FixturFab/fixture_switch_reader/images/bottom case cad.JPG

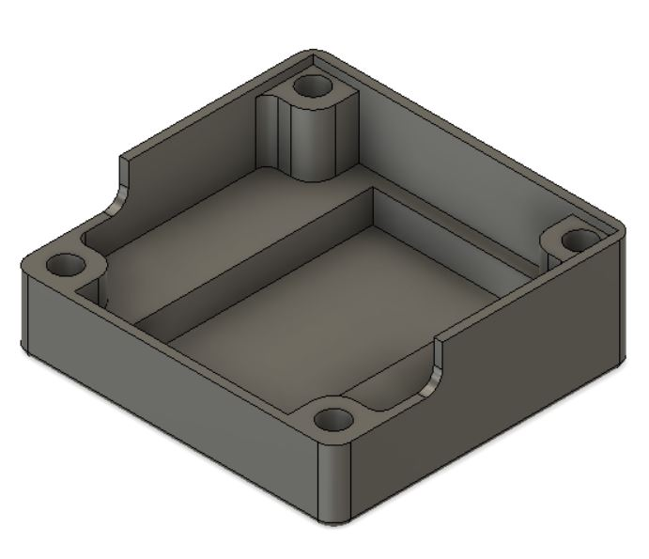
images/bottom case cad.JPG
