FixturFab/fixture_switch_reader/images/cura screenshot.JPG

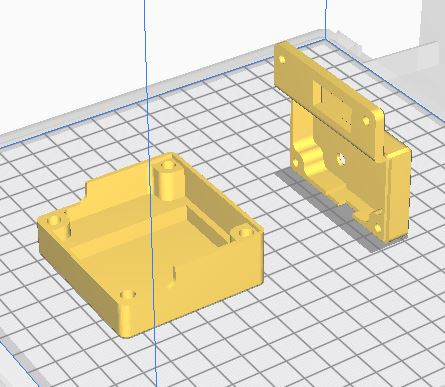
images/cura screenshot.JPG
