FixturFab/fixture_switch_reader/images/device_model.JPG

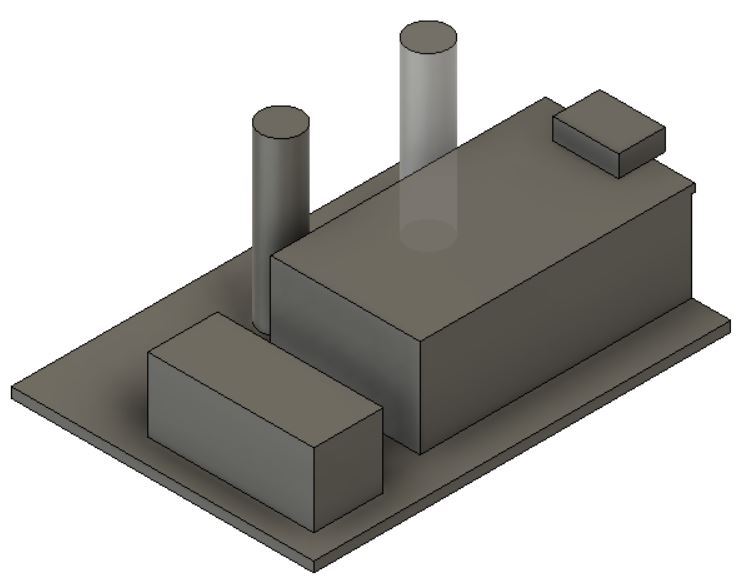
images/device_model.JPG
