FixturFab/fixture_switch_reader/images/firmware flow.png

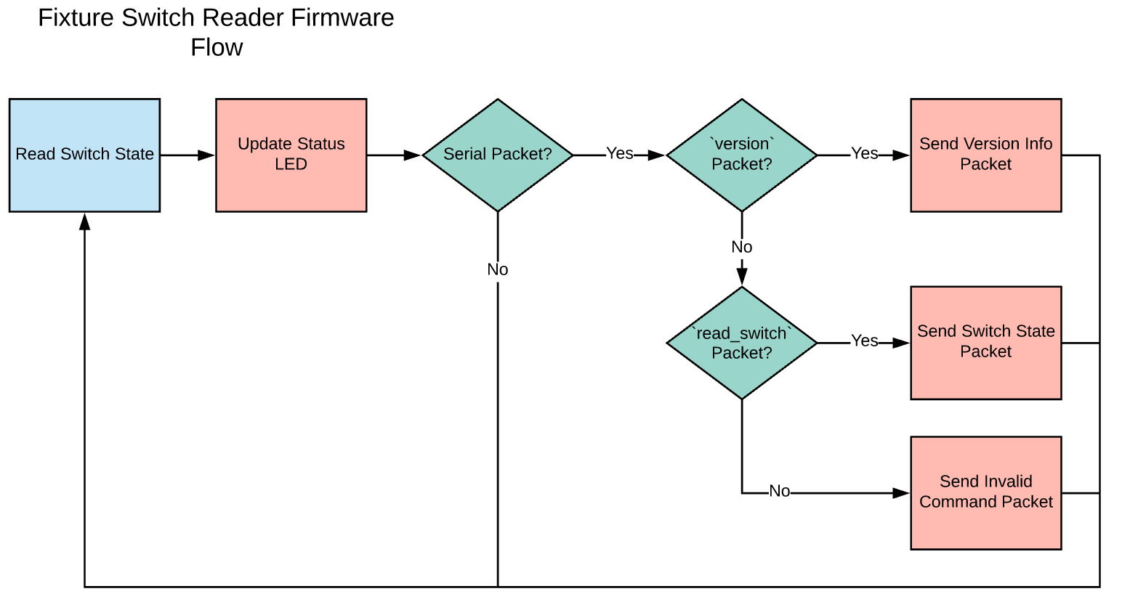
images/firmware flow.png
