FixturFab/fixture_switch_reader/images/fixture base.jpg

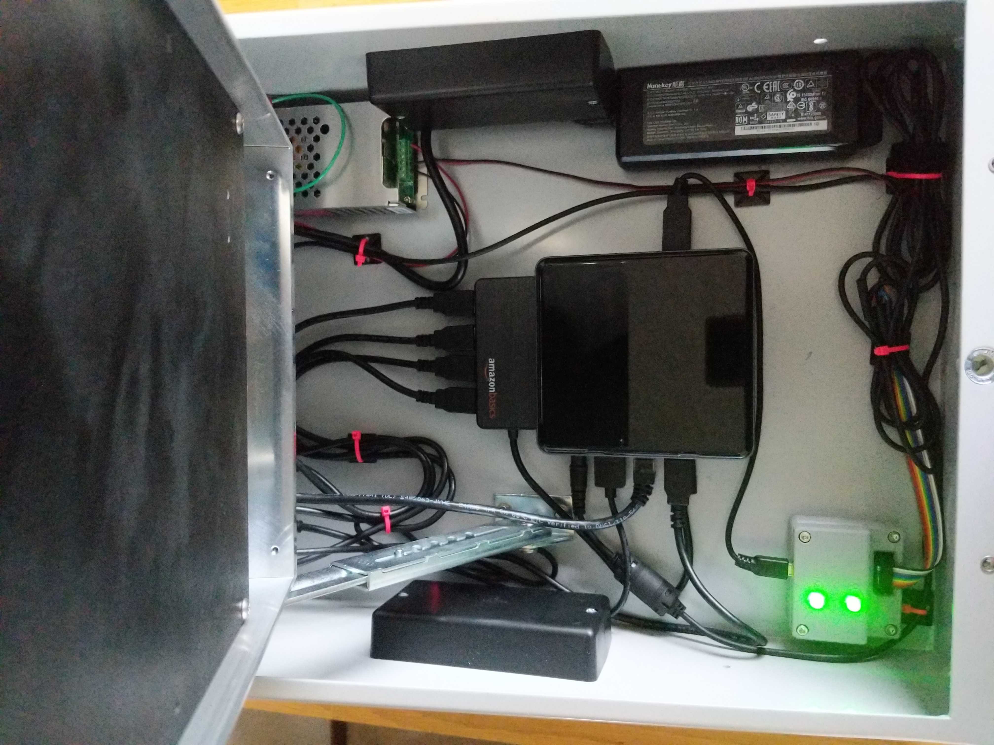
images/fixture base.jpg
