FixturFab/fixture_switch_reader/images/fixture open.jpg

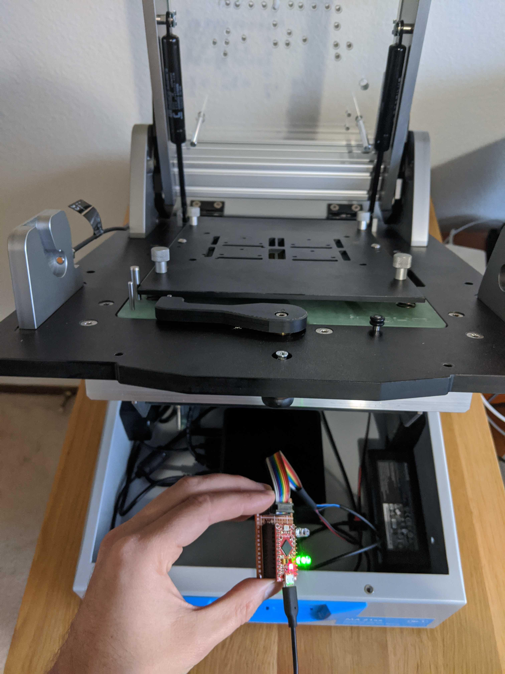
images/fixture open.jpg
