FixturFab/fixture_switch_reader/images/switch reader in fixture base.jpg

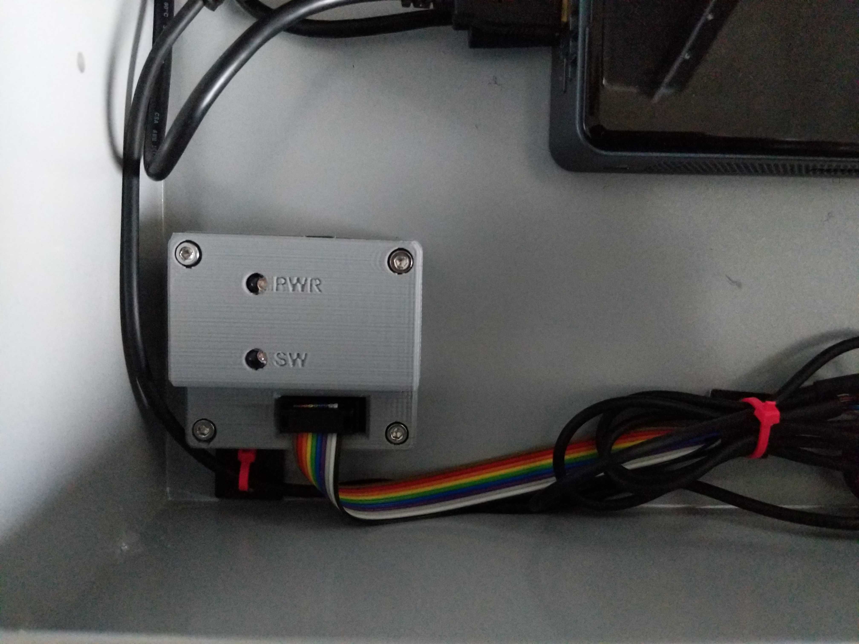
images/switch reader in fixture base.jpg
