FixturFab/fixture_switch_reader/images/top case cad.JPG

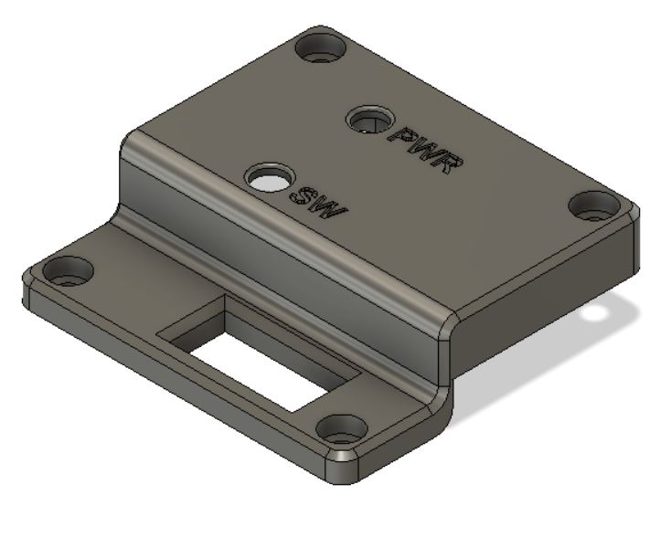
images/top case cad.JPG
