FixturFab/fixture_switch_reader/images/finale assembly parts.jpg

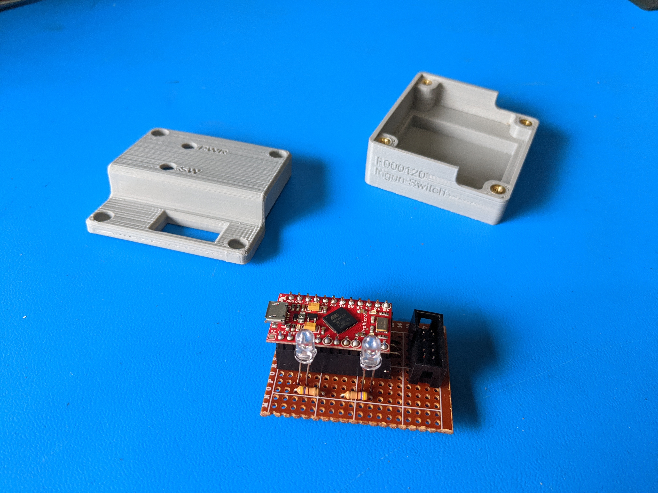
images/finale assembly parts.jpg
