FixturFab/fixture_switch_reader/images/case assembly cad.JPG

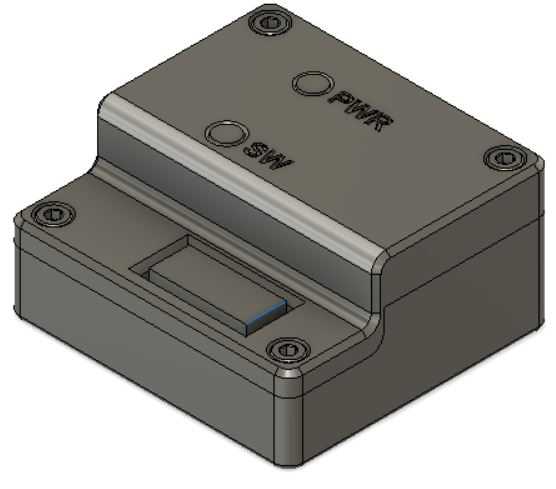
images/case assembly cad.JPG
