FixturFab/fixture_switch_reader/images/top case assembly 1.jpg

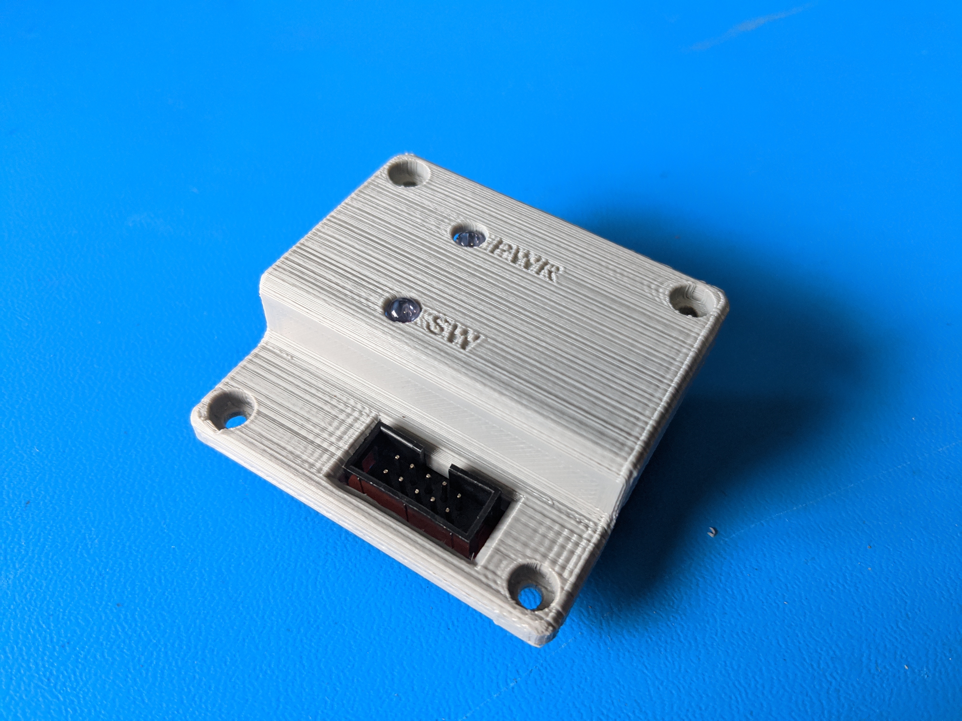
images/top case assembly 1.jpg
