FixturFab/fixture_switch_reader/images/top case assembly 2.jpg

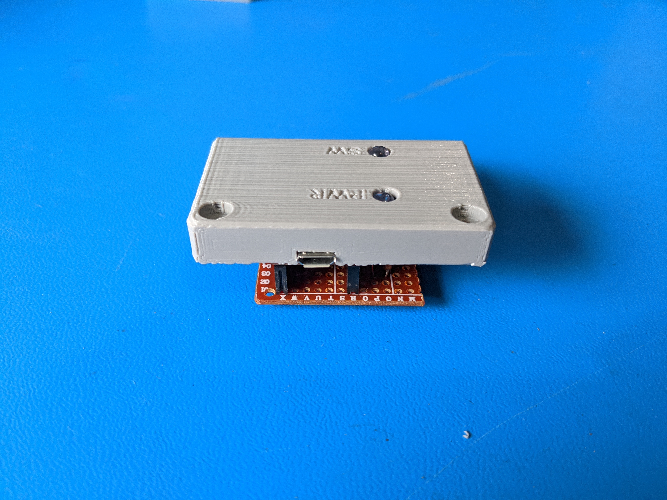
images/top case assembly 2.jpg
